pappavis/EasyLab-retro-synth-SN76489/src/commando_esp32.py

# the first 15 seconds of the chiptune Commando by Rob Hubbard and play it using 3 analoge pins on a ESP32

from machine import Pin, PWM
import time

# Define the analog pins
analog_pins = [26, 27, 32]

# Define the PWM frequency
freq = 440

# Define the PWM duty cycle
duty = 512

# Define the duration of the note
duration = 0.25

# Define the square wave function
def square_wave(freq, duty):
    return int(duty < 1024 * freq / 2)

# Initialize the PWM pins
pwms = [PWM(Pin(pin), freq=freq, duty=duty) for pin in analog_pins]

# Define the notes for the melody
notes = ['C', 'D', 'E', 'C', 'C', 'D', 'E', 'C', 'E', 'F', 'G', 'E', 'F', 'G', 'C']

# Define the durations for the melody
durations = [0.25] * 15

# Define the tempo of the melody
tempo = 120

# Define the time per beat based on the tempo
tpb = 60 / tempo

# Play the melody
for note, duration in zip(notes, durations):
    freq = 261.63 * 2 ** (ord(note) - ord('C') + 3) / 12
    for t in range(int(duration / tpb * 1000)):
        for i, pwm in enumerate(pwms):
            pwm.duty(1023 * square_wave(freq, duty))
            time.sleep_us(1000 // len(pwms))
