pappavis/EasyLab-retro-synth-SN76489/src/example_vgm.py

# Please write a class library in micropython for the ESP32 which plays a VGM-file on a SN76489 via I2C. Also, generate a suitable clock signal for the YM3812 from the ESP32 to the SN76489.
# https://chat.openai.com/chat/ede913fa-4fcb-44ae-81d8-b8f546e91327

import machine
import time
import ustruct

class SN76489:
    def __init__(self, i2c, address, clock_pin):
        self.i2c = i2c
        self.address = address
        self.clock_pin = machine.Pin(clock_pin, machine.Pin.OUT)
        
    def write(self, data):
        self.i2c.writeto(self.address, data)
        
    def write_register(self, register, value):
        self.write(bytearray([register, value]))
        
    def set_clock(self, frequency):
        self.clock_pin.freq(frequency)
        
class VGMPlayer:
    def __init__(self, i2c, sn76489_address, sn76489_clock_pin):
        self.sn76489 = SN76489(i2c, sn76489_address, sn76489_clock_pin)
        self.clock_frequency = 4000000
        self.commands = {
            0x50: self.handle_psg_command,
            0x61: self.handle_wait_command,
            # add more handlers for other VGM commands here
        }
        
    def play_vgm(self, filename):
        with open(filename, 'rb') as f:
            # read VGM file header
            header = f.read(0x40)
            # extract important information from header
            version, sn76489_clock, _, data_offset, _ = ustruct.unpack('<4sI3sI', header[0x08:0x1c])
            self.sn76489.set_clock(sn76489_clock)
            
            # seek to data section of file
            f.seek(data_offset, 0)
            while True:
                # read VGM command header (3 bytes)
                command, _, delay = ustruct.unpack('<BBH', f.read(3))
                if command not in self.commands:
                    raise ValueError('Invalid VGM command: {}'.format(hex(command)))
                # call appropriate command handler
                self.commands[command](f, delay)
            
    def handle_psg_command(self, f, delay):
        # read PSG data (4 bytes)
        data = f.read(4)
        self.sn76489.write_register(data[0], data[1])
        self.sn76489.write_register(data[0] + 1, data[2])
        
    def handle_wait_command(self, f, delay):
        time.sleep_us(delay * 62.5)
