pappavis/EasyLab-retro-synth-SN76489/src/YM3812_simplesong_esp8266.py

# Please write a program in micropython for the ESP32 which plays mary Had a Little Lamb using YM3812 via I2C. Also, generate a suitable clock signal for the YM3812 from the ESp8266 to the YM2812.

import machine
import time
from machine import Pin, I2C

# Set up the I2C bus and the YM3812 address
i2c = I2C(scl=Pin(22), sda=Pin(21))
YM3812_ADDR = 0x5A

# Set up the hardware timer for generating the clock signal
timer = machine.Timer(0)
timer.init(period=227, mode=machine.Timer.PERIODIC, callback=lambda t:Pin(25, Pin.OUT).value(not Pin(25, Pin.OUT).value()))

# Send the initialization commands to the YM3812
i2c.writeto(YM3812_ADDR, bytes([0x01, 0x20, 0x41]))
i2c.writeto(YM3812_ADDR, bytes([0x02, 0x4F]))
i2c.writeto(YM3812_ADDR, bytes([0x08, 0xF1]))

# Define the note frequencies for Mary Had a Little Lamb
C4 = 262
D4 = 294
E4 = 330
G4 = 392
A4 = 440

# Define the melody for Mary Had a Little Lamb
melody = [E4, D4, C4, D4, E4, E4, E4, D4, D4, D4, E4, E4, E4, E4, D4, C4, D4, E4, E4, E4, D4, D4, E4, D4, C4]

# Define the rhythm for Mary Had a Little Lamb
rhythm = [4, 4, 4, 4, 4, 4, 2, 4, 4, 4, 4, 4, 2, 4, 4, 4, 4, 4, 2, 4, 4, 4, 4, 4, 4]

# Play the melody on the YM3812
for note, dur in zip(melody, rhythm):
    # Set the frequency of the note
    i2c.writeto(YM3812_ADDR, bytes([0xA0, 0x00, note & 0xFF]))
    i2c.writeto(YM3812_ADDR, bytes([0xA0, 0x01, note >> 8]))
    
    # Set the duration of the note
    dur_ticks = int(dur * 7.5)
    i2c.writeto(YM3812_ADDR, bytes([0xB0, 0x00, dur_ticks]))
    i2c.writeto(YM3812_ADDR, bytes([0xB0, 0x01, dur_ticks >> 8]))
    
    # Wait for the note to finish
    time.sleep(dur / 2)
